fernandezdelpeloso/stm32-nixie-clock/media/images/DSC00113.JPG

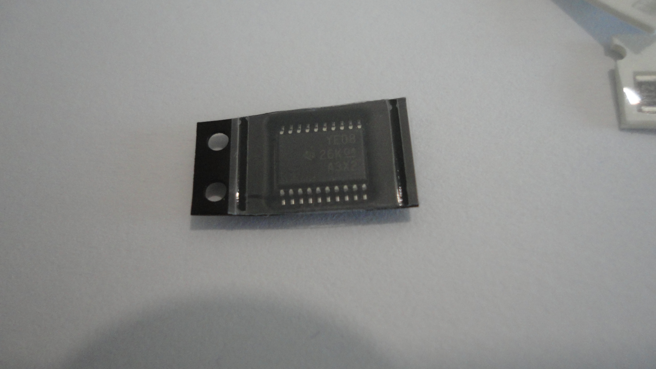
media/images/DSC00113.JPG
