fernandezdelpeloso/stm32-nixie-clock/media/images/DSC00114.JPG

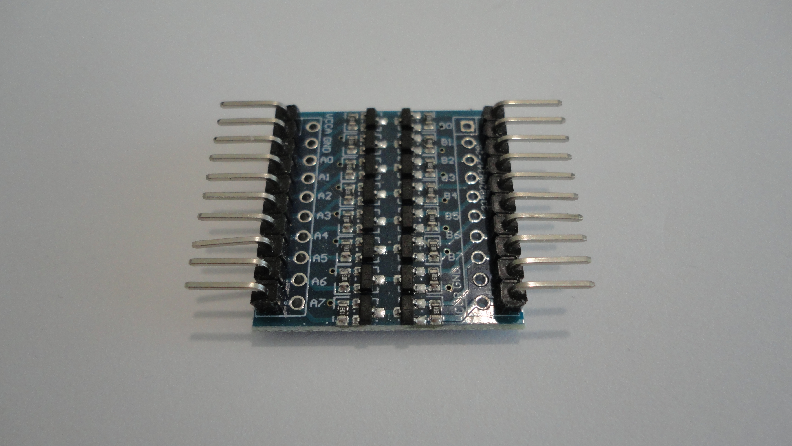
media/images/DSC00114.JPG
