fernandezdelpeloso/stm32-nixie-clock/media/images/DSC00115.JPG

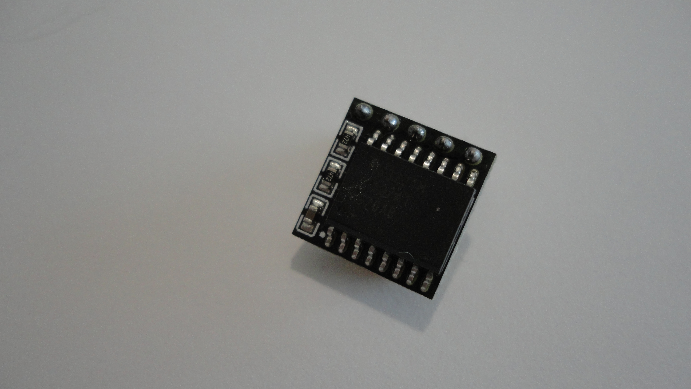
media/images/DSC00115.JPG
