fernandezdelpeloso/stm32-nixie-clock/media/images/DSC00117.JPG

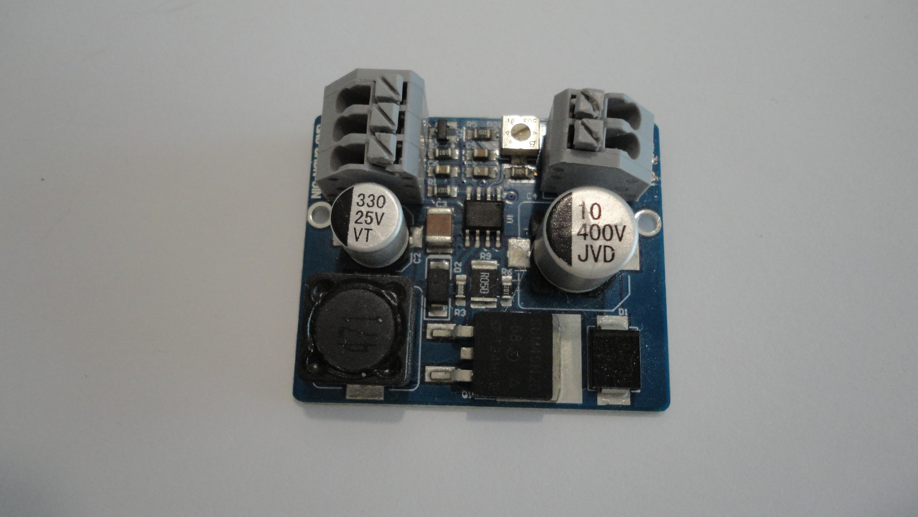
media/images/DSC00117.JPG
