fernandezdelpeloso/stm32-nixie-clock/media/images/DSC00118.JPG

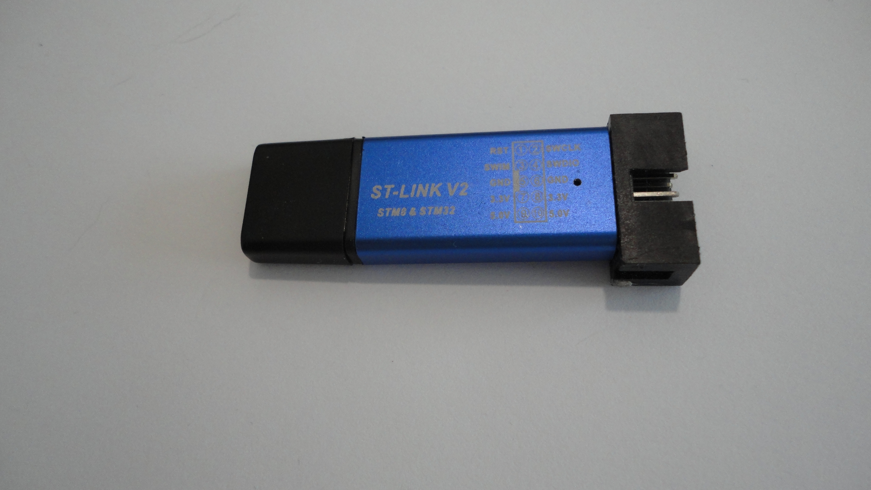
media/images/DSC00118.JPG
