fernandezdelpeloso/stm32-nixie-clock/media/images/DSC00119.JPG

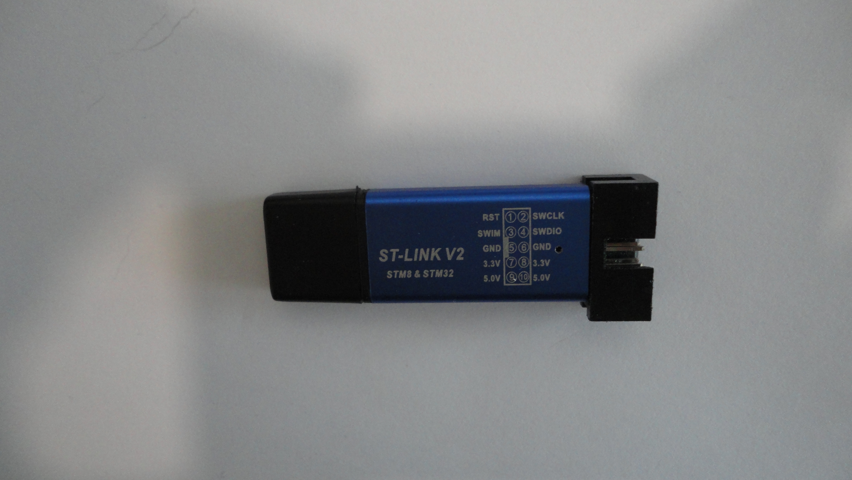
media/images/DSC00119.JPG
