fernandezdelpeloso/stm32-nixie-clock/media/images/DSC00122.JPG

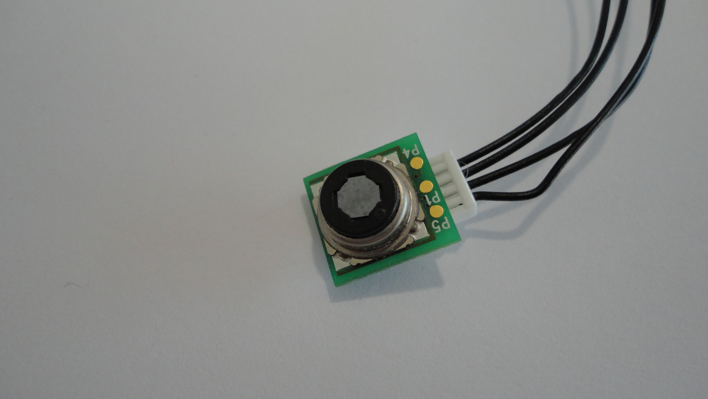
media/images/DSC00122.JPG
