fernandezdelpeloso/stm32-nixie-clock/media/images/DSC00123.JPG

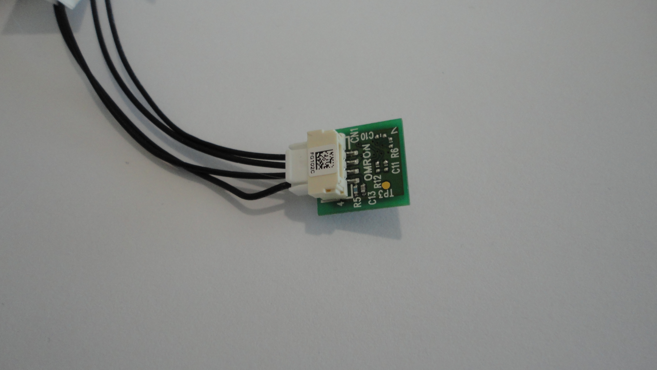
media/images/DSC00123.JPG
